streamin/Weather-Forcasting-ESP8266-Infinity-Mirror/Photos/2016-03-13 19.41.28.jpg

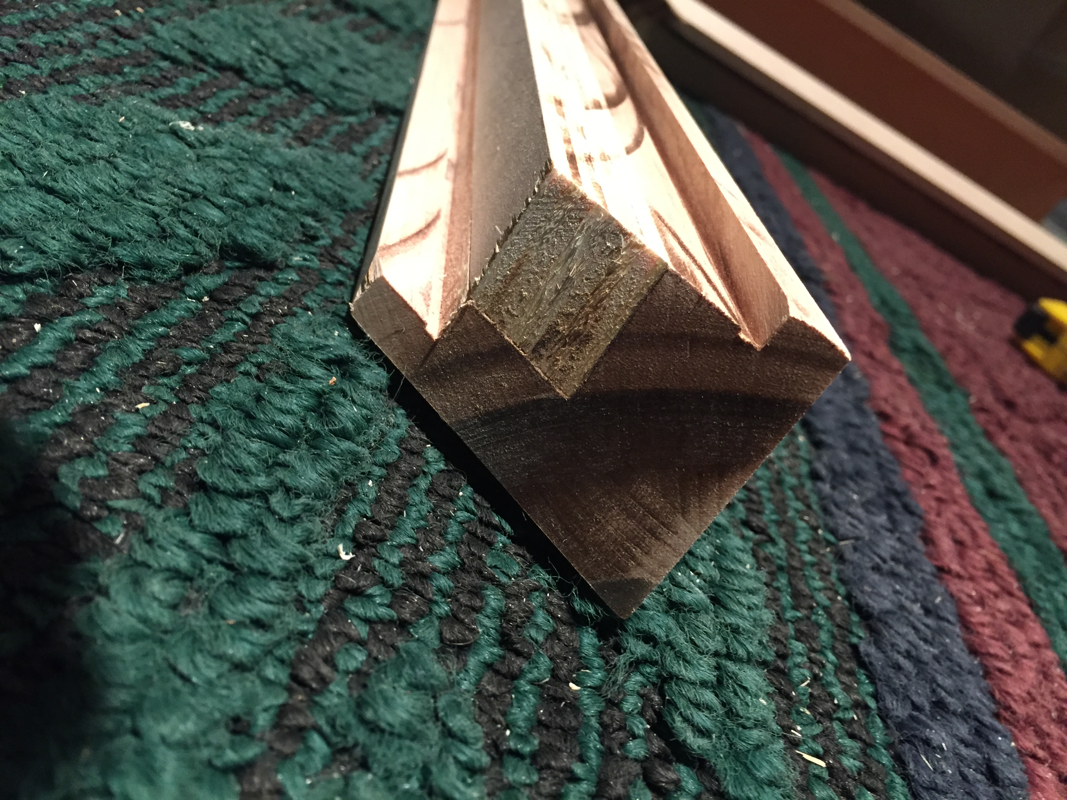
Photos/2016-03-13 19.41.28.jpg
